Stanislav-developer/Rear_Bike_Light/Materials/KiCad_Circuit/ATtiny13_Rear_Bike_Light/ATtiny13_Rear_Bike_Light.kicad_sch

## KiCad design Materials/KiCad_Circuit/ATtiny13_Rear_Bike_Light/ATtiny13_Rear_Bike_Light.kicad_sch (2025-07-05)

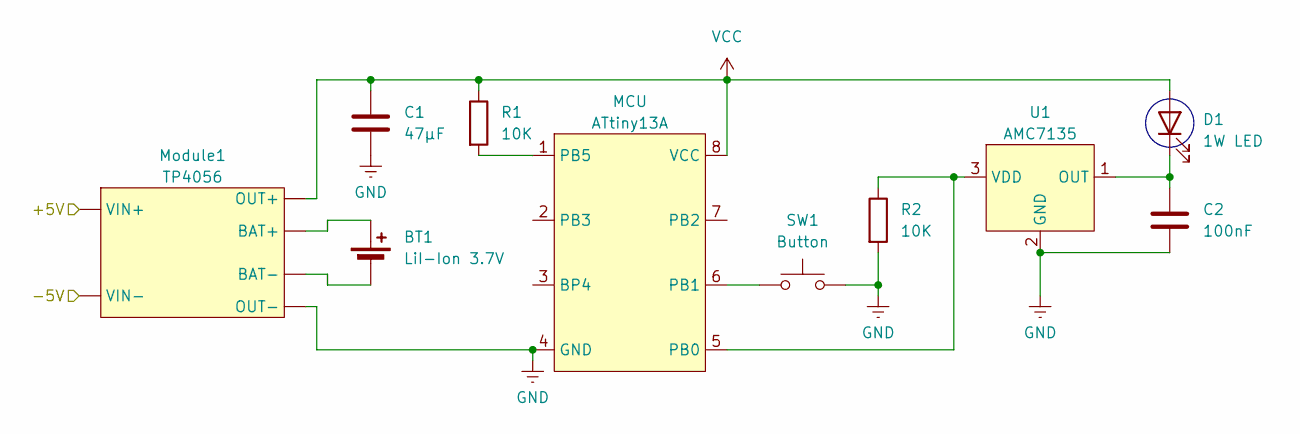
[picture p33: schematic ATtiny13_Rear_Bike_Light.kicad_sch]

Parts:
BT1: LiI-Ion 3.7V
C1: 47μF
C2: 100nF
D1: 1W LED
MCU: ATtiny13A
Module1: TP4056
R1, R2: 10K
SW1: Button
U1: AMC7135

Connections:
+5V: Module1.
-5V: Module1.
GND: C1.2, C2.2, MCU.4 (GND), Module1., R2.2, SW1.2, U1.2 (GND)
unnamed: BT1.1 (+), Module1.
unnamed: BT1.2 (-), Module1.
unnamed: C2.1, D1.1 (K), U1.1 (OUT)
unnamed: MCU.1 (PB5), R1.2
unnamed: MCU.5 (PB0), R2.1, U1.3 (VDD)
unnamed: MCU.6 (PB1), SW1.1
VCC: C1.1, D1.2 (A), MCU.8 (VCC), Module1., R1.1
